noah-yacowar/AI-MU-Motion-Capture/Hardware/Case/V2/Holder_V2.2.SLDPRT

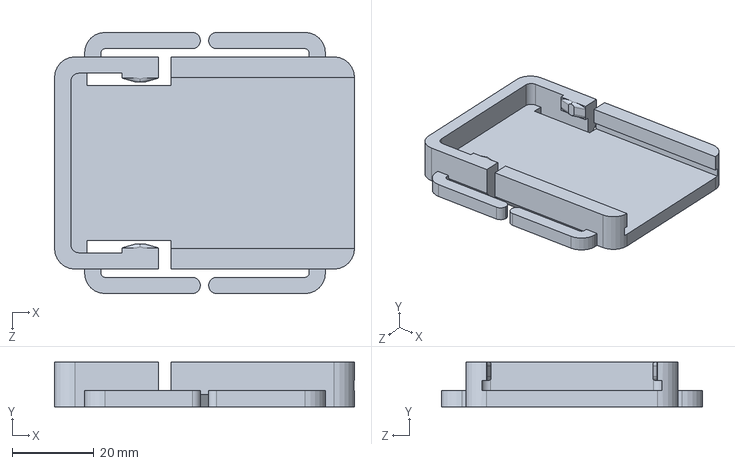
[picture p22: CAD file, 2025-09-02]
Hardware/Case/V2/Holder_V2.2.SLDPRT
73.5 x 11.0 x 64.0 mm
