noah-yacowar/AI-MU-Motion-Capture/Hardware/Case/V2/Top_Unstretched.SLDPRT

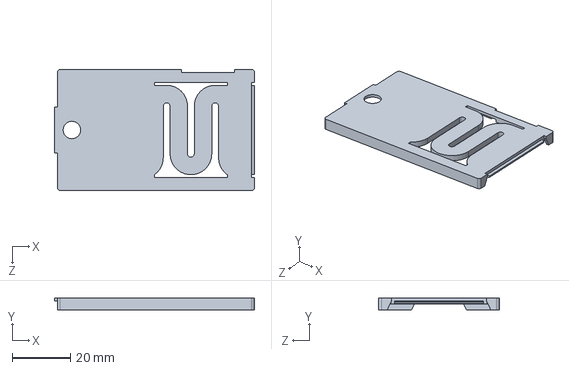
[picture p23: CAD file, 2025-09-02]
Hardware/Case/V2/Top_Unstretched.SLDPRT
68.4 x 4.00 x 41.4 mm
